kinoshita-lab/Fruit-Mochi-Exciter/soft/src/debug.h

/********************************** (C) COPYRIGHT
 ******************************** File Name          : debug.h Author : WCH
 * Version            : V1.0.0
 * Date               : 2022/08/08
 * Description        : This file contains all the functions prototypes for UART
 *                      Printf , Delay functions.
 *********************************************************************************
 * Copyright (c) 2021 Nanjing Qinheng Microelectronics Co., Ltd.
 * Attention: This software (modified or not) and binary are used for
 * microcontroller manufactured by Nanjing Qinheng Microelectronics.
 *******************************************************************************/
#ifndef __DEBUG_H
#define __DEBUG_H

#ifdef __cplusplus
extern "C" {
#endif


void SDI_Printf_Enable(void);

#ifdef __cplusplus
}
#endif

#endif /* __DEBUG_H */
